davidmcgookin/Haju/illustrative_images/IMG_2712.JPG

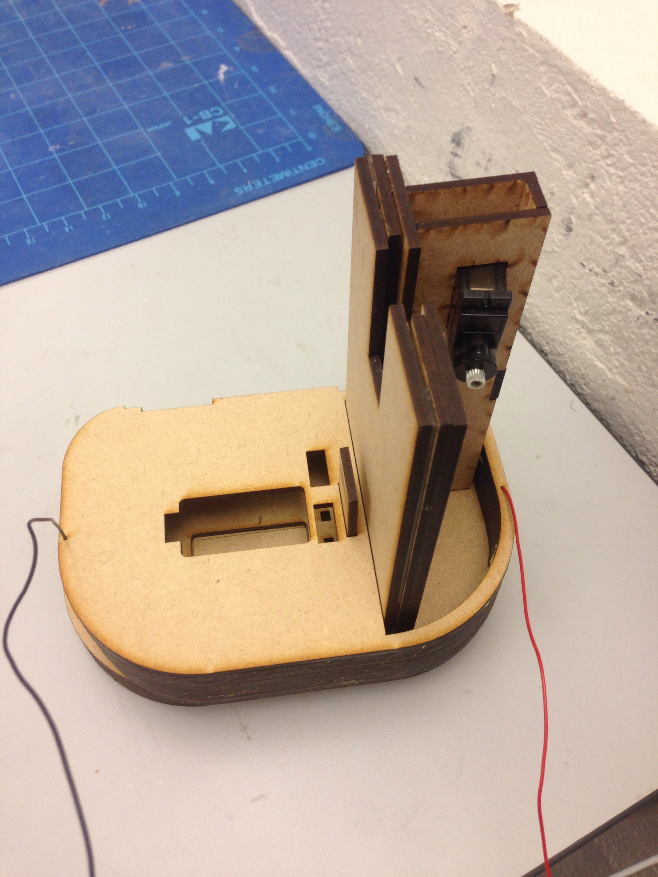
illustrative_images/IMG_2712.JPG
