davidmcgookin/Haju/illustrative_images/IMG_2720.JPG

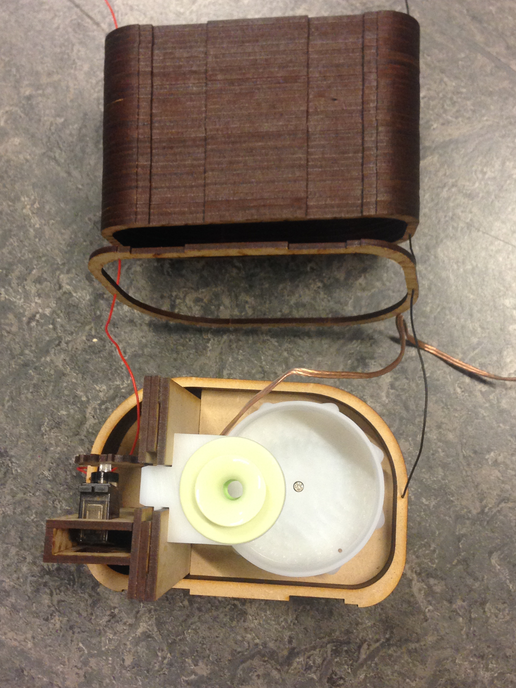
illustrative_images/IMG_2720.JPG
