davidmcgookin/Haju/illustrative_images/IMG_2722.JPG

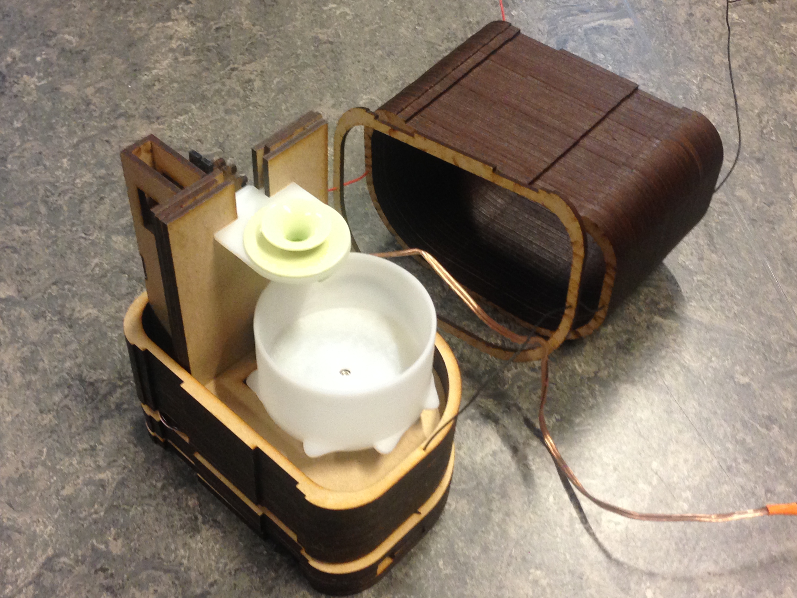
illustrative_images/IMG_2722.JPG
