davidmcgookin/Haju/illustrative_images/IMG_2739.JPG

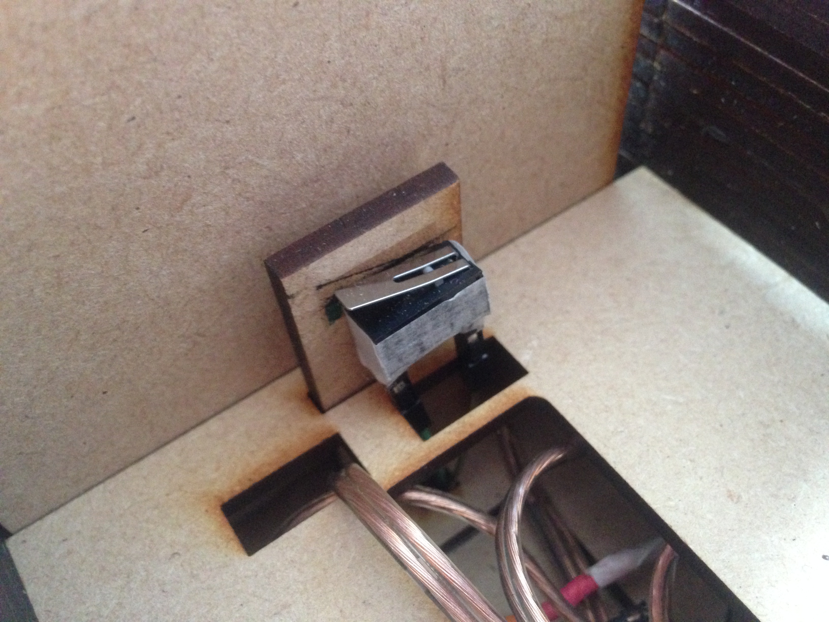
illustrative_images/IMG_2739.JPG
